MOB0926/Custom-Wired-Wireless-Keyboard/Journal/image-4.png

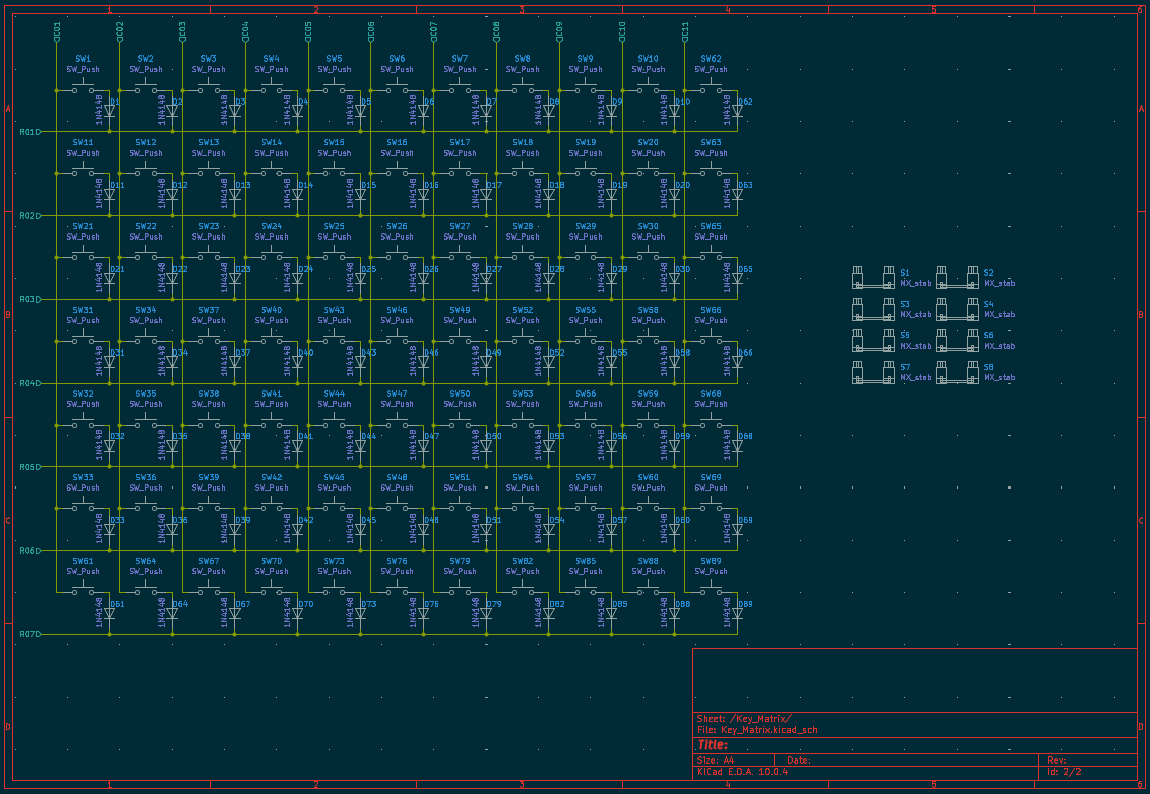
Journal/image-4.png
